hjf/ReflowOven/Arduino files/ReflowOvenController/config.h

#define HARDWARE_SPI
#ifndef HARDWARE_SPI
#define MISO 14
#define MOSI 12
#define MCLK 16
#endif
#define TC1_CS 4
#define TC2_CS 5
#define DISPLAY_CS 13
#define KEYBOARD_CS 2
#define TRIAC_ENABLE 2
#define LED1 1
#define LED2 3
#define TRIAC_PERIOD 200

#define PID_sampleTime 10000


//#define MISO 14
//#define MOSI 12
//#define MCLK 16
//#define TC1_CS 4
//#define TC2_CS 5
//#define DISPLAY_CS 13
//#define KEYBOARD_CS 2
//#define TRIAC_ENABLE 15
//#define LED1 1
//#define LED2 3
